YueWang996/Wheeled-Legged-Robot/src/LowPass.h

//
// Created by Justin on 18/03/2022.
// Reference: https://github.com/curiores/ArduinoTutorials/blob/main/LowPass2.0/LowPass2.0.ino
//

#ifndef FOCX_LOWPASS_H
#define FOCX_LOWPASS_H

#define _SQRT2 1.41421356237f

template <int order>
class LowPass{
private:
    float a[order];
    float b[order+1];
    float omega0;
    float dt;
    bool adapt;
    float tn1 = 0;
    float x[order+1]; // Raw values
    float y[order+1]; // Filtered values

public:
    ///
    /// \param f0 cutoff frequency (Hz)
    /// \param fs sample frequency (Hz)
    /// \param adaptive boolean flag, if set to 1, the code will automatically set the sample frequency based on the time history.
    LowPass(float f0, float fs, bool adaptive){
        omega0 = 6.28318530718f*f0;
        dt = 1.0f/fs;
        adapt = adaptive;
        tn1 = -dt;
        for(int k = 0; k < order+1; k++){
            x[k] = 0;
            y[k] = 0;
        }
        setCoef();
    }

    void setCoef(){
        if(adapt){
            float t = micros()/1.0e6;
            dt = t - tn1;
            tn1 = t;
        }

        float alpha = omega0*dt;
        if(order==1){
            a[0] = -(alpha - 2.0)/(alpha+2.0);
            b[0] = alpha/(alpha+2.0);
            b[1] = alpha/(alpha+2.0);
        }
        if(order==2){
            float c1 = 2*_SQRT2/alpha;
            float c2 = 4/(alpha*alpha);
            float denom = 1.0+c1+c2;
            b[0] = 1.0/denom;
            b[1] = 2.0/denom;
            b[2] = b[0];
            a[0] = -(2.0-2.0*c2)/denom;
            a[1] = -(1.0-c1+c2)/(1.0+c1+c2);
        }
    }

    float filter(float xn){
        // Provide me with the current raw value: x
        // I will give you the current filtered value: y
        if(adapt){
            setCoef(); // Update coefficients if necessary
        }
        y[0] = 0;
        x[0] = xn;
        // Compute the filtered values
        for(int k = 0; k < order; k++){
            y[0] += a[k]*y[k+1] + b[k]*x[k];
        }
        y[0] += b[order]*x[order];

        // Save the historical values
        for(int k = order; k > 0; k--){
            y[k] = y[k-1];
            x[k] = x[k-1];
        }

        // Return the filtered value
        return y[0];
    }
};


#endif //FOCX_LOWPASS_H
